AFKWarrior28/ClassDAmp/KiCad Files/KiCad Assets/3dmodels/USB4125-GF-A_REVA2.step

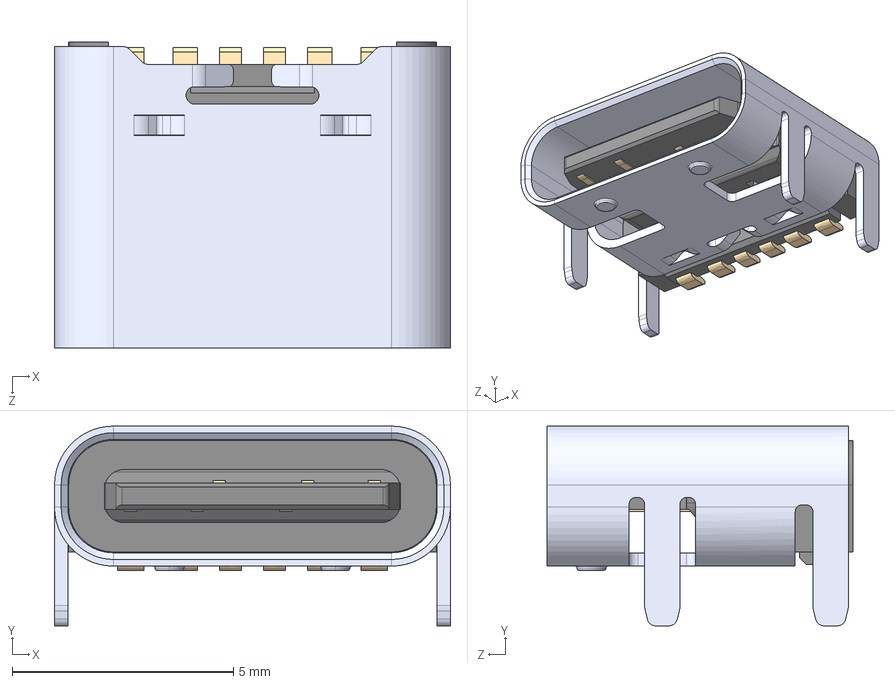
[picture p15: CAD file, 2025-12-02]
KiCad Files/KiCad Assets/3dmodels/USB4125-GF-A_REVA2.step
8.94 x 4.51 x 6.90 mm
