AFKWarrior28/ClassDAmp/KiCad Files/KiCad Assets/3dmodels/CAP_PKPZ_12P5X20_LOW_RUB.step

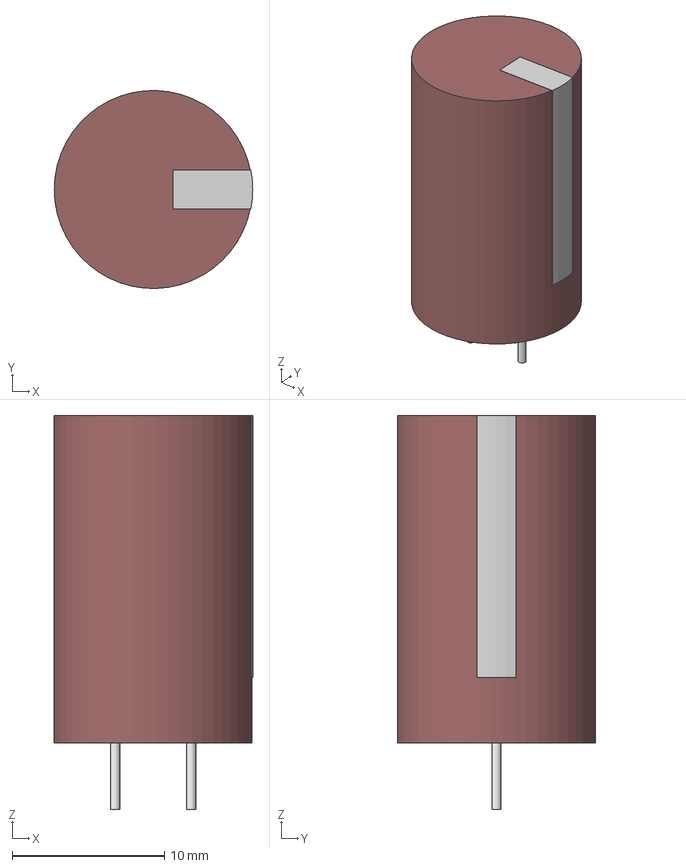
[picture p16: CAD file, 2025-12-02]
KiCad Files/KiCad Assets/3dmodels/CAP_PKPZ_12P5X20_LOW_RUB.step
13.0 x 13.0 x 25.9 mm
