AFKWarrior28/ClassDAmp/KiCad Files/KiCad Assets/3dmodels/2N4401.STEP

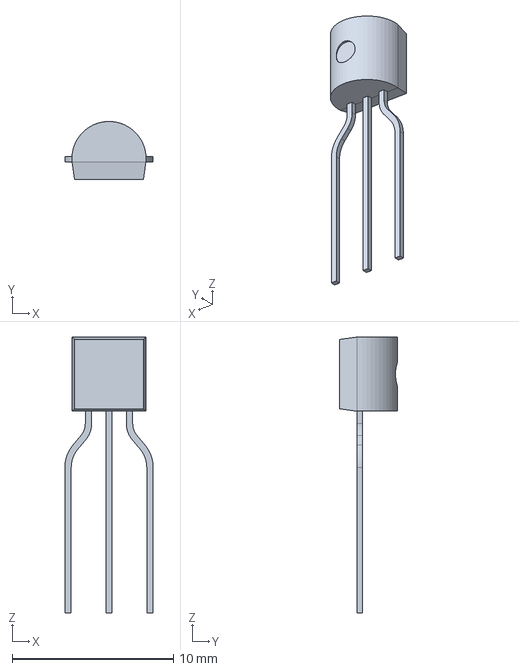
[picture p17: CAD file, 2025-12-02]
KiCad Files/KiCad Assets/3dmodels/2N4401.STEP
5.48 x 3.60 x 17.1 mm
